pellematrose/ESP32-C3_Sensor/Hardware/ESP32-C3_Sensor/source_2026-02-19/3dmodels/R_0805_2012Metric.step

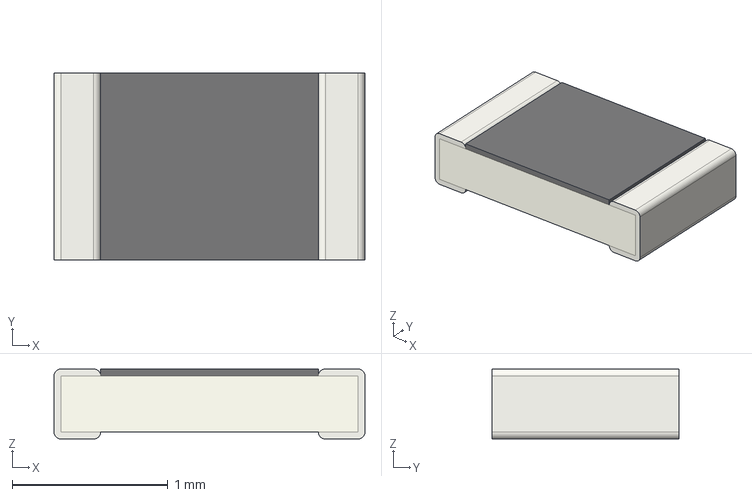
[picture p15: CAD file, 2026-02-18]
Hardware/ESP32-C3_Sensor/source_2026-02-19/3dmodels/R_0805_2012Metric.step
2.00 x 1.20 x 0.45 mm
