pellematrose/ESP32-C3_Sensor/Hardware/ESP32-C3_Sensor/source_2026-02-19/3dmodels/D_SOD-523.step

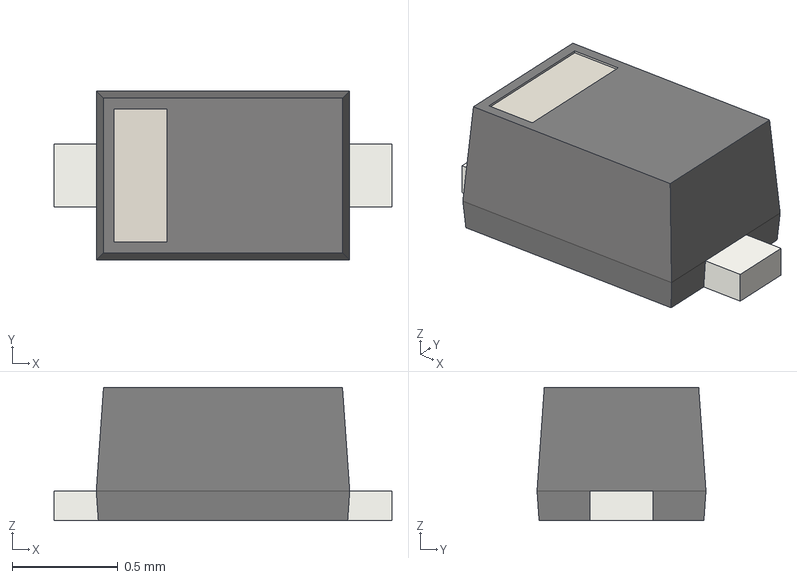
[picture p16: CAD file, 2026-02-18]
Hardware/ESP32-C3_Sensor/source_2026-02-19/3dmodels/D_SOD-523.step
1.60 x 0.8 x 0.63 mm
