pellematrose/ESP32-C3_Sensor/Hardware/ESP32-C3_Sensor/source_2026-02-19/3dmodels/SOT-23-6.step

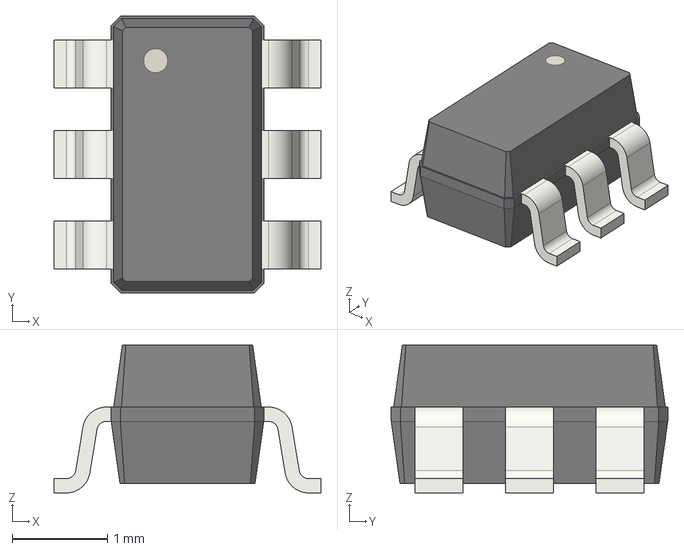
[picture p18: CAD file, 2026-02-18]
Hardware/ESP32-C3_Sensor/source_2026-02-19/3dmodels/SOT-23-6.step
2.80 x 2.90 x 1.55 mm
