pellematrose/ESP32-C3_Sensor/Hardware/ESP32-C3_Sensor/source_2026-02-19/3dmodels/USB_C_Receptacle_GCT_USB4105-xx-A_16P_TopMnt_Horizontal.step

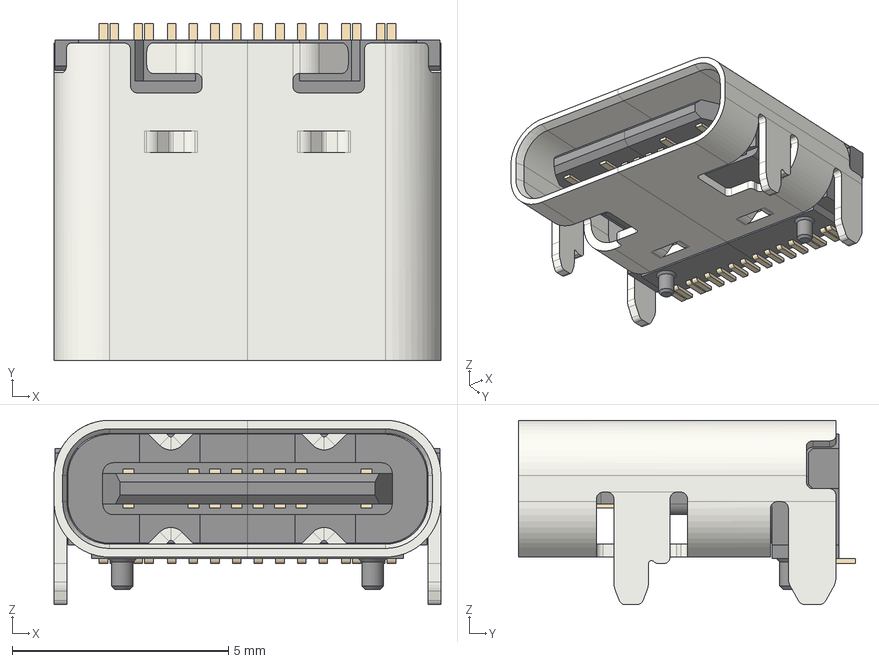
[picture p19: CAD file, 2026-02-18]
Hardware/ESP32-C3_Sensor/source_2026-02-19/3dmodels/USB_C_Receptacle_GCT_USB4105-xx-A_16P_TopMnt_Horizontal.step
8.94 x 7.78 x 4.26 mm
