pellematrose/ESP32-C3_Sensor/Hardware/ESP32-C3_Sensor/source_2026-02-19/3dmodels/LED_0603_1608Metric.step

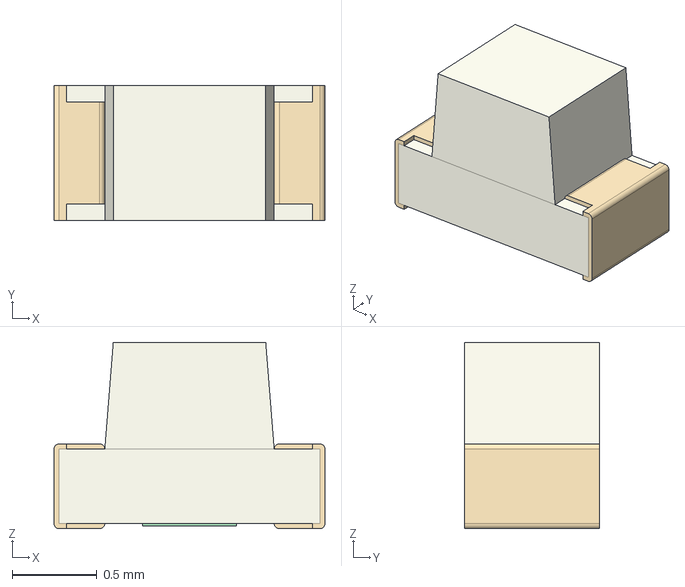
[picture p21: CAD file, 2026-02-18]
Hardware/ESP32-C3_Sensor/source_2026-02-19/3dmodels/LED_0603_1608Metric.step
1.60 x 0.8 x 1.10 mm
