pellematrose/ESP32-C3_Sensor/FW/wizard20201120/wizard/src/mongoose_fs.c

#include "mongoose.h"

#if defined(__cplusplus)
extern "C" {
#endif
const char *mg_unlist(size_t no);
const char *mg_unpack(const char *, size_t *, time_t *);
#if defined(__cplusplus)
}
#endif

static const unsigned char v1[] = {
  31, 139,   8,   0,   0,   0,   0,   0,   0,   3, 172, 125, // ...........}
 123, 119, 218, 198, 246, 232, 223, 247, 126,  10, 172, 147, // {w......~...
  75, 165,  50,  96, 192, 143,  56,  34,  19,  86, 142, 147, // K.2`..8".V..
 212,  57, 141, 147,  52, 142, 211,  54,  28, 159,  44,   1, // .9..4..6..,.
   3, 168,  22,  18, 149, 132,  31,  53, 220, 207, 126, 247, // .......5..~.
  99, 102,  36,   1, 238, 105, 127, 235, 118, 165,  98,  52, // cf$..i..v.b4
 207,  61, 251,  53, 123, 239, 153, 145, 159, 239, 189, 250, // .=.5{.......
 112, 250, 249, 215, 143, 175, 107, 179, 124,  30, 189, 120, // p.....k.|..x
  62,  87, 121,  80,  27, 205, 130,  52,  83, 185,  92, 230, // >WyP...4S...
 147, 230, 137, 206, 139, 131, 185, 146,  55, 161, 186,  93, // ........7..]
  36, 105,  94,  27,  37, 113, 174, 226,  92,  58, 183, 225, // $i^.%q...:..
  56, 159, 201, 177, 186,   9,  71, 170,  73,  47, 162,  22, // 8.....G.I/..
 198,  97,  30,   6,  81,  51,  27,   5, 145, 146, 157,  86, // .a..Q3.....V
 219, 121, 241,  60,  10, 227, 235,  90, 170,  34,  25,  66, // .y.<...Z.".B
 211, 218,  44,  85,  19,  25,  37, 211, 164, 149, 221,  76, // ..,U..%....L
 107, 249, 253,  66, 201, 112,  30,  76, 213,  62, 188,  54, // k..B.p.L.>.6
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
  70,  28,  83, 202, 168, 140,  12, 204,  15, 170, 117, 149, // F.S.......u.
 126,  17,  14, 234, 191,  14, 147, 197,  48, 187, 172, 171, // ~.......0...
 250,  51, 125, 156, 153, 228, 107,  24,   3, 208, 239, 163, // .3}...k.....
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
