pellematrose/ESP32-C3_Sensor/FW/wizard/wifi_manager.h

/*
 * SPDX-License-Identifier: MIT
 *
 * Copyright (c) 2026 Per-Simon Saal
 */
#pragma once
#include <PubSubClient.h>
#include <WiFi.h>
#include "storage.h"

extern PubSubClient client; 
extern WiFiClient thermoClient; 


struct Cred {
  char ssid[25];
  char pass[25];
};
extern Cred c;

struct md {
  bool en;
  char broker[50];
  char topic_pressure[30];
  char topic_batvol[30];
  char topic_temp2[30];
  char topic_temp1[30];
};
extern md mqttdata;

void connect_wifi();
void open_ap();
void start_webserver();

void mqtt_setup();
void mqtt_reconnect();
void mqtt_callback(char* topic, byte* message, unsigned int length);
void mqtt_publish();
void mqtt_loop();
