pellematrose/ESP32-C3_Sensor/FW/wizard/oled_gui.h

/*
 * SPDX-License-Identifier: MIT
 *
 * Copyright (c) 2026 Per-Simon Saal
 */
 
#include <U8g2lib.h>

void oled_hello();
void oled_data(float, float, float);
void oled_auxdata(uint32_t); // TODO: add ip address
void oled_off();
